Lafudoci/ProbeCube/Arduino with cc3000wifi based/3Dprint_part/pc_shield_3d_v1.JPG

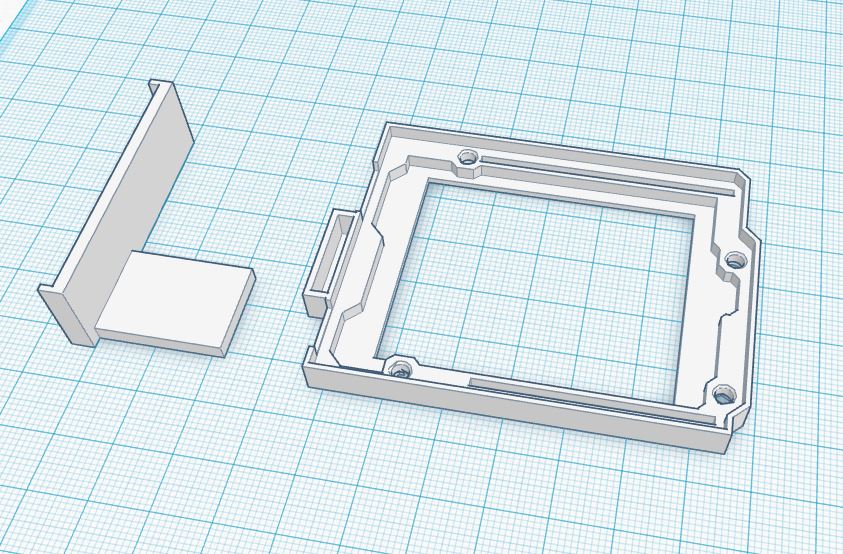
Arduino with cc3000wifi based/3Dprint_part/pc_shield_3d_v1.JPG
