Lafudoci/ProbeCube/Arduino with cc3000wifi based/Fritzing_sketch/ProbeCube_Nano/ProbeCube_nano_v1_bb.png

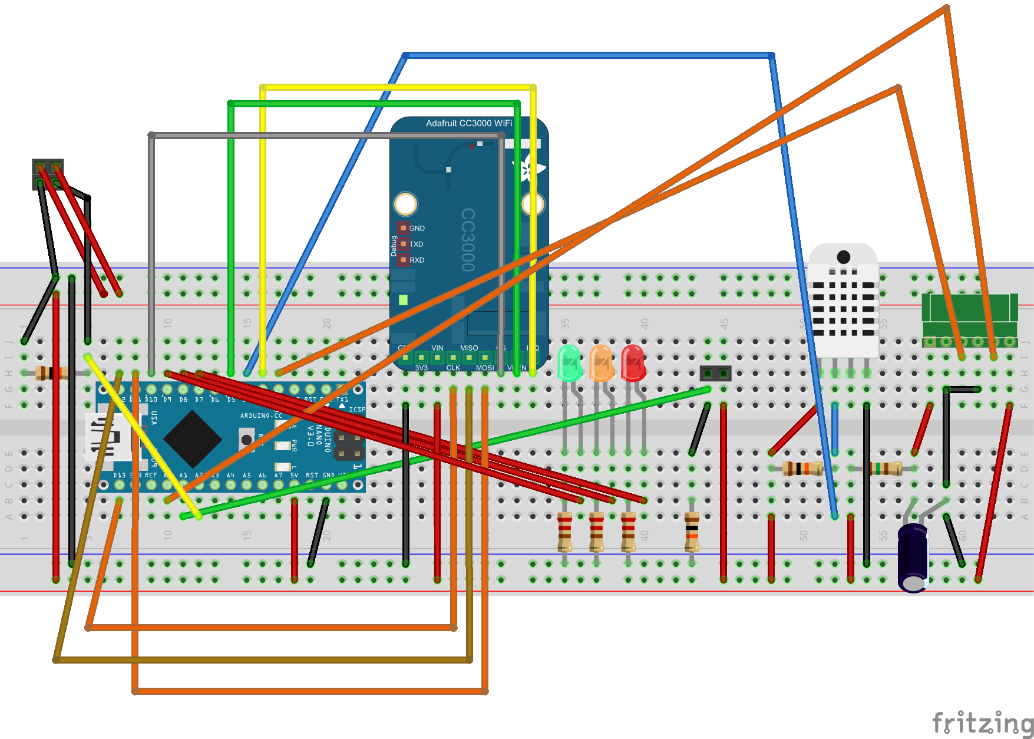
Arduino with cc3000wifi based/Fritzing_sketch/ProbeCube_Nano/ProbeCube_nano_v1_bb.png
