Lafudoci/ProbeCube/Particle Photon based/Fritzing_sketch/BOM材料表.png

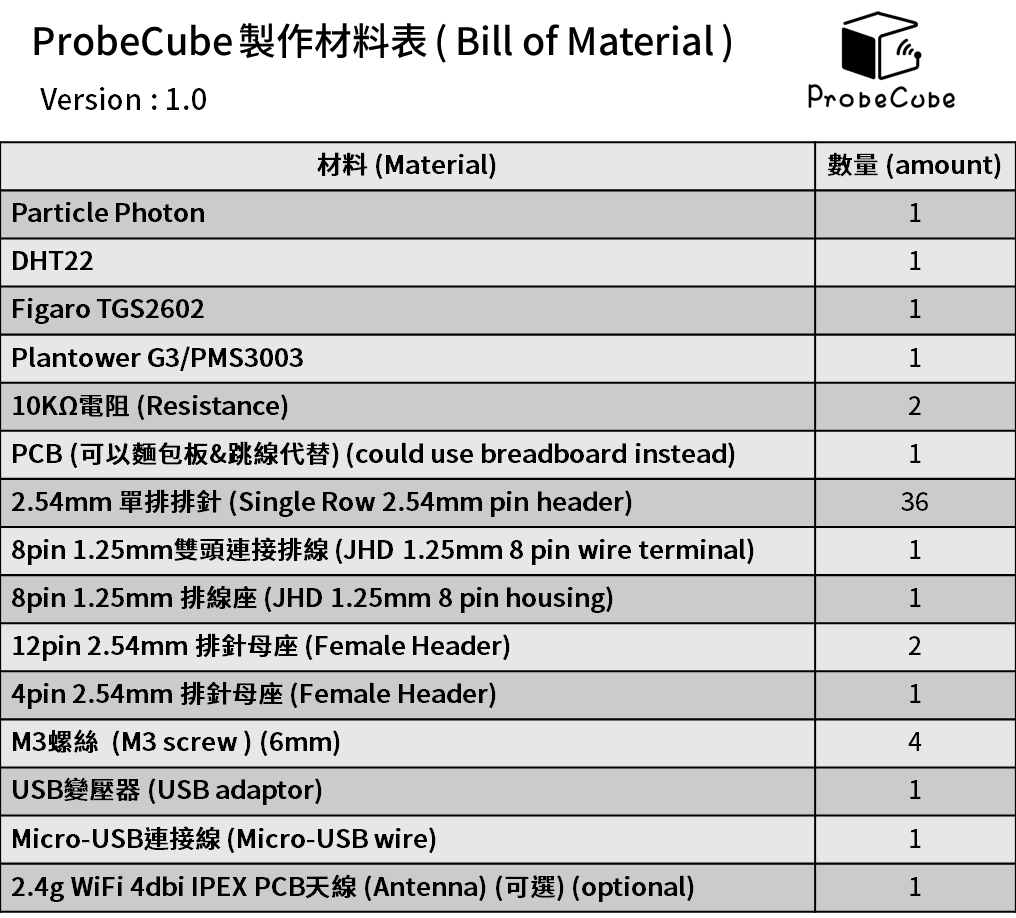
Particle Photon based/Fritzing_sketch/BOM材料表.png
